mdlougheed/Beefy-3/Photos/20181228_105209.jpg

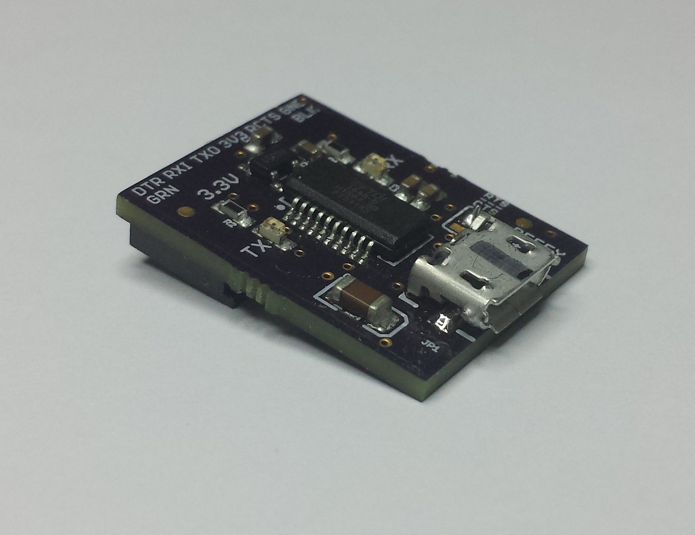
Photos/20181228_105209.jpg
