mdlougheed/Beefy-3/Photos/20181228_105246.jpg

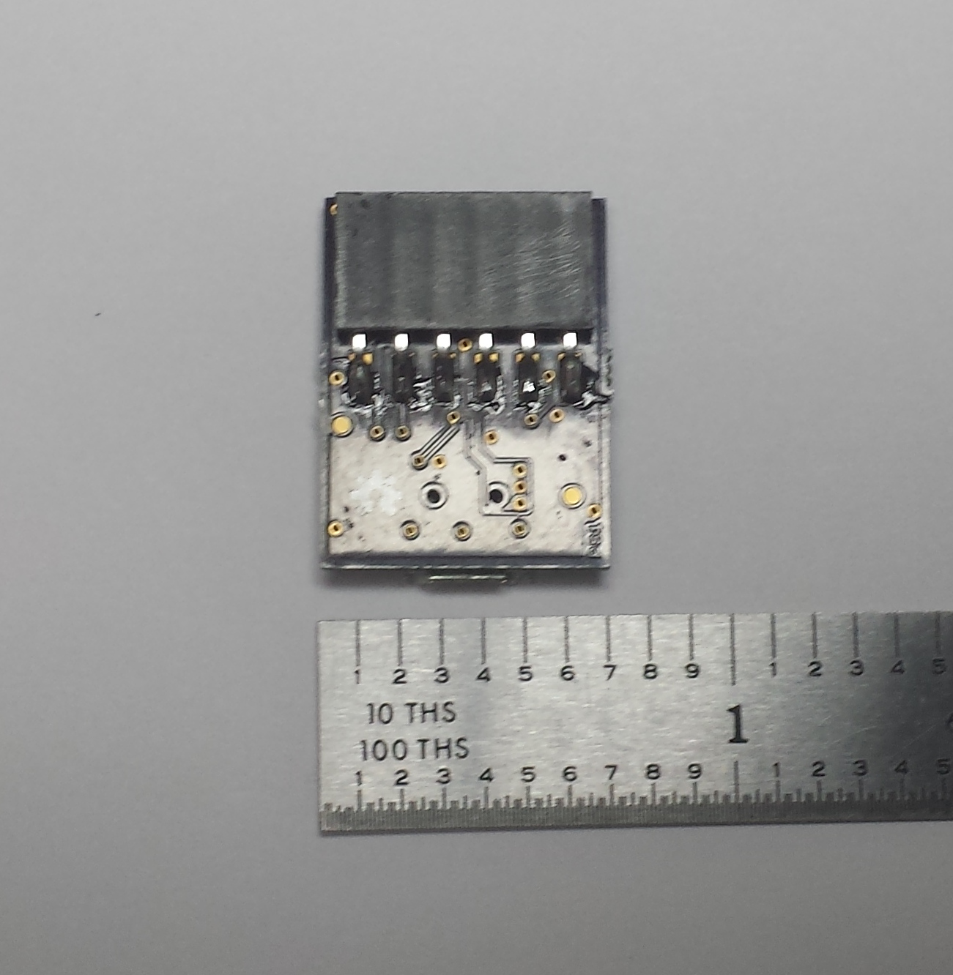
Photos/20181228_105246.jpg
